molwam/Automaton-169/pcb/kicad files/rule169.kicad_sch

## KiCad design pcb/kicad files/rule169.kicad_sch (2022-12-21)

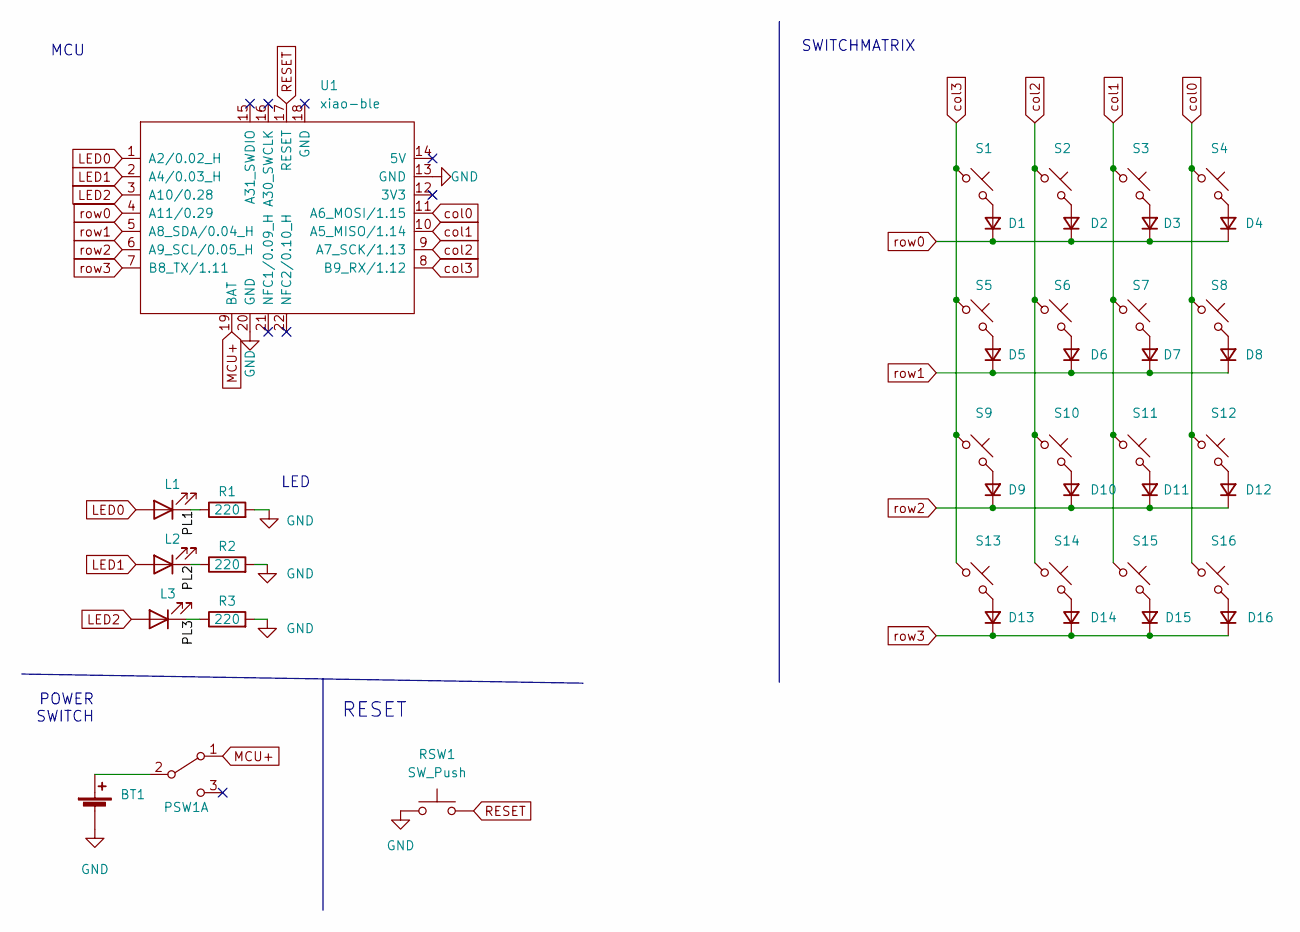
[picture p15: schematic rule169.kicad_sch]

Parts:
BT1: Battery_Cell; JST_PH_reversible
D1, D2, D3, D4, D5, D6, D7, D8, D9, D10, D11, D12, D13, D14, D15, D16: D_Small; Diode_SOD123
L1, L2, L3: LED; LED_3mm_reversible
PSW1: SW_DPDT_x2; MSK12C02_reversible
R1, R2, R3: 220; R_1206_DoubleSided
RSW1: SW_Push; ResetSW
S1, S2, S3, S4, S5, S6, S7, S8, S9, S10, S11, S12, S13, S14, S15, S16: MX_SW_HS; Kailh_socket_PG1350_optional_reversible
U1: xiao-ble; xiao seed ble

Connections:
GND: BT1.2 (-), R1.2, R2.2, R3.2, RSW1.1, U1.13 (GND), U1.20 (GND)
LED0: L1.2 (A), U1.1 (A2/0.02_H)
LED1: L2.2 (A), U1.2 (A4/0.03_H)
LED2: L3.2 (A), U1.3 (A10/0.28)
MCU+: PSW1.1 (A), U1.19 (BAT)
unnamed: BT1.1 (+), PSW1.2 (B)
unnamed: D1.2 (A), S1.2
unnamed: D2.2 (A), S2.2
unnamed: D3.2 (A), S3.2
unnamed: D4.2 (A), S4.2
unnamed: D5.2 (A), S5.2
unnamed: D6.2 (A), S6.2
unnamed: D7.2 (A), S7.2
unnamed: D8.2 (A), S8.2
unnamed: D9.2 (A), S9.2
unnamed: D10.2 (A), S10.2
unnamed: D11.2 (A), S11.2
unnamed: D12.2 (A), S12.2
unnamed: D13.2 (A), S13.2
unnamed: D14.2 (A), S14.2
unnamed: D15.2 (A), S15.2
unnamed: D16.2 (A), S16.2
PL1: L1.1 (K), R1.1
PL2: L2.1 (K), R2.1
PL3: L3.1 (K), R3.1
RESET: RSW1.2, U1.17 (RESET)
col0: S4.1, S8.1, S12.1, S16.1, U1.11 (A6_MOSI/1.15)
col1: S3.1, S7.1, S11.1, S15.1, U1.10 (A5_MISO/1.14)
col2: S2.1, S6.1, S10.1, S14.1, U1.9 (A7_SCK/1.13)
col3: S1.1, S5.1, S9.1, S13.1, U1.8 (B9_RX/1.12)
row0: D1.1 (K), D2.1 (K), D3.1 (K), D4.1 (K), U1.4 (A11/0.29)
row1: D5.1 (K), D6.1 (K), D7.1 (K), D8.1 (K), U1.5 (A8_SDA/0.04_H)
row2: D9.1 (K), D10.1 (K), D11.1 (K), D12.1 (K), U1.6 (A9_SCL/0.05_H)
row3: D13.1 (K), D14.1 (K), D15.1 (K), D16.1 (K), U1.7 (B8_TX/1.11)

Notes on the sheet:
RESET
POWER SWITCH
MCU
SWITCHMATRIX
LED
